charles-lyc/Pindar/hardware/datasheet/esp32/20200527125322933.jpg

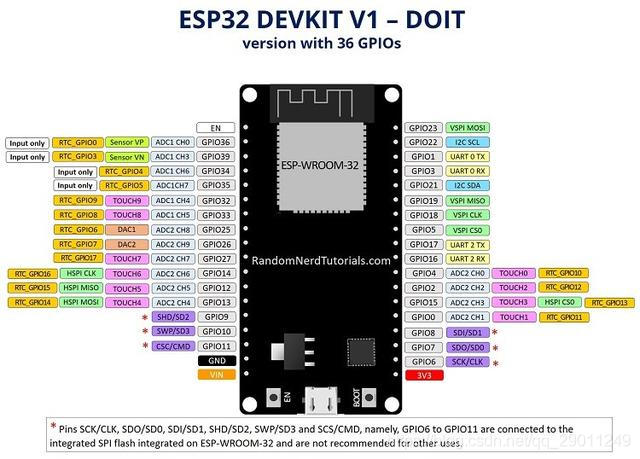
hardware/datasheet/esp32/20200527125322933.jpg
