charles-lyc/Pindar/hw/kicad/app/motor/dc_motor/dc_motor_x3.kicad_sch

## KiCad design hw/kicad/app/motor/dc_motor/dc_motor_x3.kicad_sch (2023-06-30)

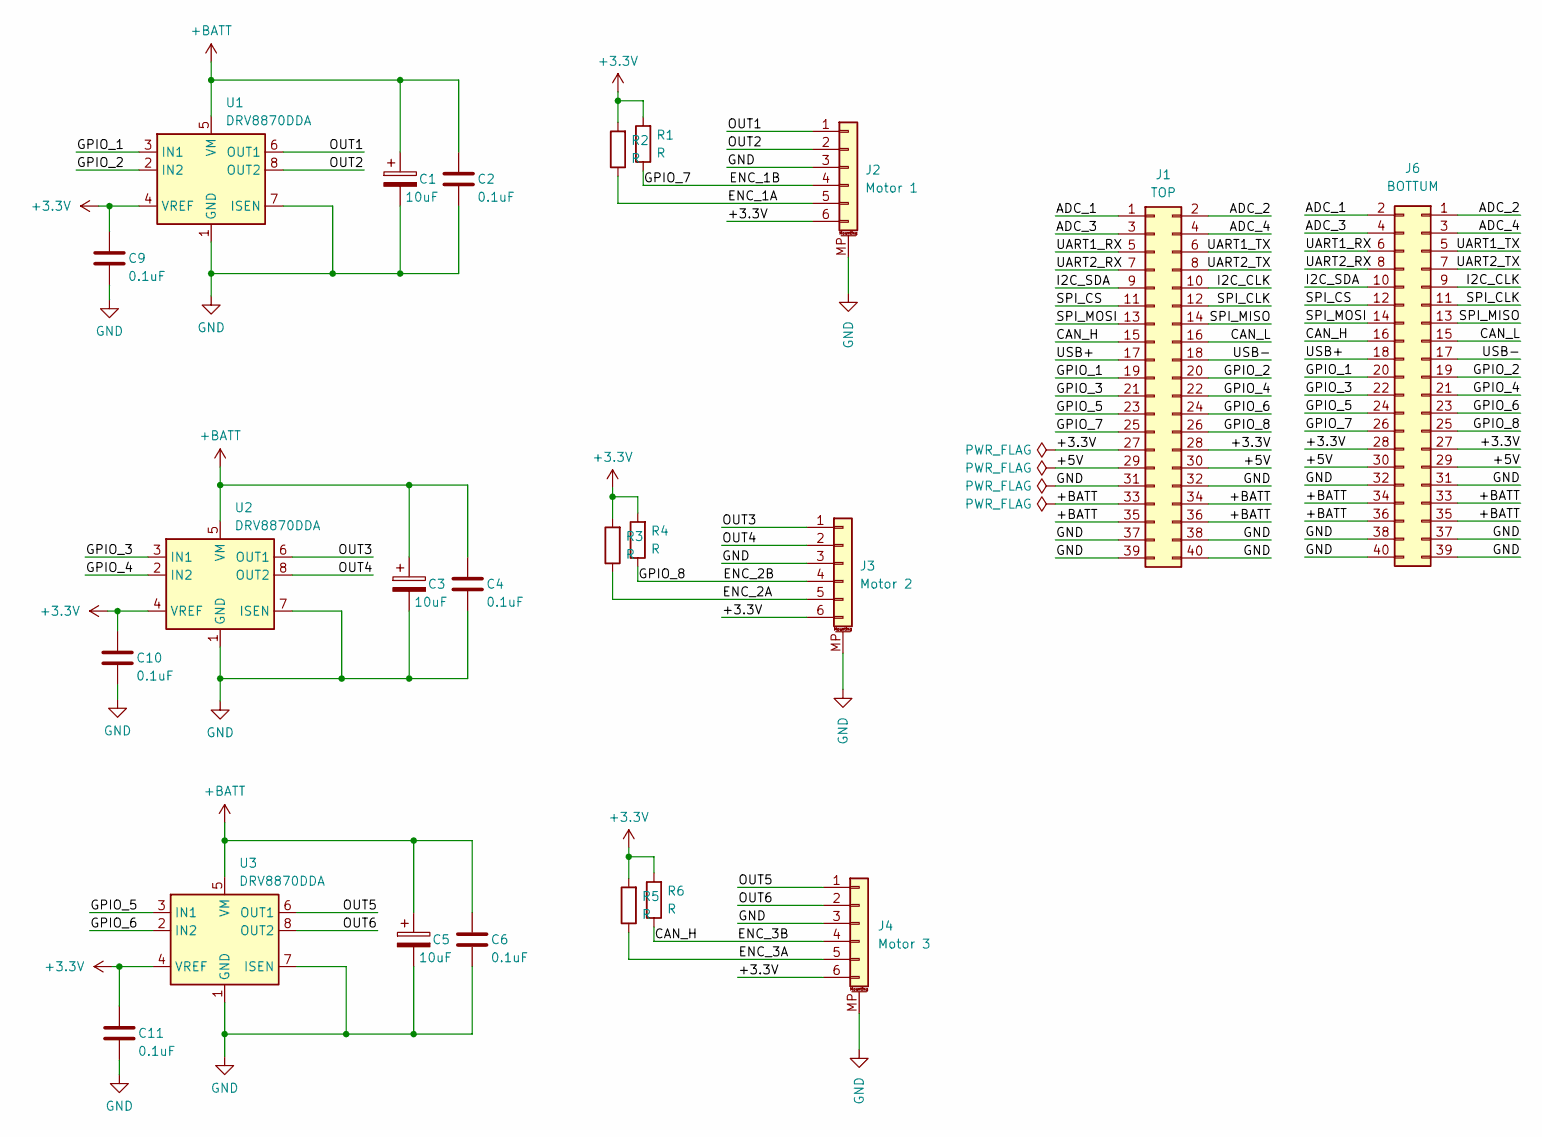
[picture p36: schematic dc_motor_x3.kicad_sch]

Parts:
C1, C3, C5: 10uF; CP_Elec_6.3x5.4
C2, C4, C6, C9, C10, C11: 0.1uF; C_0805_2012Metric
J1: TOP; PinHeader_2x20_P1.27mm_Vertical_SMD
J2: Motor 1; JST_GH_SM06B-GHS-TB_1x06-1MP_P1.25mm_Horizontal
J3: Motor 2; JST_GH_SM06B-GHS-TB_1x06-1MP_P1.25mm_Horizontal
J4: Motor 3; JST_GH_SM06B-GHS-TB_1x06-1MP_P1.25mm_Horizontal
J6: BOTTUM; PinHeader_2x20_P1.27mm_Vertical_SMD
R1, R2, R3, R4, R5, R6: R; R_0805_2012Metric
U1, U2, U3: DRV8870DDA; Texas_HTSOP-8-1EP_3.9x4.9mm_P1.27mm_EP2.95x4.9mm_Mask2.4x3.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

Connections:
+3.3V: C9.1, C10.1, C11.1, J1.27, J1.28, J2.6, J3.6, J4.6, J6.27, J6.28, R1.2, R2.2, R3.2, R4.2, R5.2, R6.2, U1.4 (VREF), U2.4 (VREF), U3.4 (VREF)
+5V: J1.29, J1.30, J6.29, J6.30
+BATT: C1.1, C2.1, C3.1, C4.1, C5.1, C6.1, J1.33, J1.34, J1.35, J1.36, J6.33, J6.34, J6.35, J6.36, U1.5 (VM), U2.5 (VM), U3.5 (VM)
ADC_1: J1.1, J6.2
ADC_2: J1.2, J6.1
ADC_3: J1.3, J6.4
ADC_4: J1.4, J6.3
CAN_H: J1.15, J4.4, J6.16, R6.1
CAN_L: J1.16, J6.15
ENC_1A: J2.5, R2.1
ENC_1B: J1.25, J2.4, J6.26, R1.1
ENC_2A: J3.5, R3.1
ENC_2B: J1.26, J3.4, J6.25, R4.1
ENC_3A: J4.5, R5.1
GND: C1.2, C2.2, C3.2, C4.2, C5.2, C6.2, C9.2, C10.2, C11.2, J1.31, J1.32, J1.37, J1.38, J1.39, J1.40, J2.3, J2.MP (MountPin), J3.3, J3.MP (MountPin), J4.3, J4.MP (MountPin), J6.31, J6.32, J6.37, J6.38, J6.39, J6.40, U1.1 (GND), U1.7 (ISEN), U1.9 (GND), U2.1 (GND), U2.7 (ISEN), U2.9 (GND), U3.1 (GND), U3.7 (ISEN), U3.9 (GND)
GPIO_1: J1.19, J6.20, U1.3 (IN1)
GPIO_2: J1.20, J6.19, U1.2 (IN2)
GPIO_3: J1.21, J6.22, U2.3 (IN1)
GPIO_4: J1.22, J6.21, U2.2 (IN2)
GPIO_5: J1.23, J6.24, U3.3 (IN1)
GPIO_6: J1.24, J6.23, U3.2 (IN2)
I2C_CLK: J1.10, J6.9
I2C_SDA: J1.9, J6.10
OUT1: J2.1, U1.6 (OUT1)
OUT2: J2.2, U1.8 (OUT2)
OUT3: J3.1, U2.6 (OUT1)
OUT4: J3.2, U2.8 (OUT2)
OUT5: J4.1, U3.6 (OUT1)
OUT6: J4.2, U3.8 (OUT2)
SPI_CLK: J1.12, J6.11
SPI_CS: J1.11, J6.12
SPI_MISO: J1.14, J6.13
SPI_MOSI: J1.13, J6.14
UART1_RX: J1.5, J6.6
UART1_TX: J1.6, J6.5
UART2_RX: J1.7, J6.8
UART2_TX: J1.8, J6.7
USB+: J1.17, J6.18
USB-: J1.18, J6.17
