charles-lyc/Pindar/firmware/components/module/imu.cpp

#include "freertos/FreeRTOS.h"
#include "freertos/task.h"
#include "freertos/semphr.h"

#include "esp_system.h"
#include "esp_log.h"

#include "imu.h"
#include "param.h"

IMU_Module::IMU_Module(IMU_Interface *itf)
{
	interface = itf;

	if (interface->probe()) {
		// throw std::invalid_argument("Value must be positive");
		while (1)
			;
	}
	interface->initialize();

	// create shared memory in iram
	// sm_data = (struct SM_ImuData *)malloc(sizeof(struct SM_ImuData));

	frame_event = xSemaphoreCreateBinary();

	// Note: 正在尝试直接将成员函数作为任务函数传递，而成员函数具有额外的隐式参数（即 this 指针），导致类型不匹配。这里的process_task方法是一个非静态成员函数，而非静态成员函数在调用时需要通过一个实例来访问
	// 方法一：使用静态中间函数并传递实例，这里其实是强行利用了xTaskCreate()可以给task带参这个设定，把实例当作参数传递进去
	xTaskCreate(&IMU_Module::process_task_static, "process_task", 4096, this, 3, &process_task_handle);
	// 方法二：使用std::bind
	// 方法三：lambda表达式（类似方法一）
	// xTaskCreate(CALLBACK_LAMBDA_VOID(IMU_Module, process_task), "process_task", 4096, this, 3, &process_task_handle);

}

IMU_Module::~IMU_Module()
{
	// interface.deinit(&interface);

	// xTaskDelete();
	// xSemaphoreDelete();
}

void IMU_Module::frame_event_isr(void *arg)
{
	timestamp = xTaskGetTickCountFromISR();
	// ESP_LOGI("IMU Module", "timestamp: %d", (uint32_t)timestamp);
	xSemaphoreGiveFromISR(frame_event, NULL);
}

void IMU_Module::process_task(void *pvParameters)
{
	while (1) {
		xSemaphoreTake(frame_event, 1);
		{
			// ll read
			if (interface->read_raw_data(gyro_raw, accel_raw, temperature_raw)) {
				ESP_LOGE("IMU Module", "read failed");
				continue;
			}

			pre_process();

			// madgwick complemental filter
			madgwick_update();
		}
	}
}

void IMU_Module::pre_process()
{
	// lpf
	for (size_t i = 0; i < 3; i++) {
		gyro_smooth[i] = gyro_raw[i];
		accel_smooth[i] = accel_raw[i];
	}

	// physical
	temperature = (float)temperature_raw[0] / 132.48 + 25;
	// ESP_LOGI("IMU Module", "raw gyro: %d %d %d", gyro_raw[0], gyro_raw[1], gyro_raw[2]);
	// ESP_LOGI("IMU Module", "raw accel: %d %d %d", accel_raw[0], accel_raw[1], accel_raw[2]);
	// ESP_LOGI("IMU Module", "raw temp: %f", temperature);
	// std::cout
	for (size_t i = 0; i < 3; i++) {
		gyro[i] = (gyro_smooth[i] - gyro_bias[i]) * gyro_scale[i];
		accel[i] = (accel_smooth[i] - accel_bias[i]) * accel_scale[i];
	}
}

void IMU_Module::madgwick_update()
{
}

void IMU_Module::gyro_static_calibr_task(void *pvParameters)
{
	TickType_t last_timestamp = 0;

	while (run_gyro_static_calibr) {
		if (timestamp != last_timestamp) {
			last_timestamp = timestamp;
		}

		vTaskDelay(100 / portTICK_PERIOD_MS);
	}

	// stop
}

void IMU_Module::gyro_z_scale_calibr_task(void *pvParameters)
{

	while (run_gyro_scale_calibr) {
		// calc gyro
		vTaskDelay(100 / portTICK_PERIOD_MS);
	}

	// stop
}

void IMU_Module::aceel_sphere_calibr_task(void *pvParameters)
{

	while (run_accel_calibr) {
		// calc gyro
		vTaskDelay(100 / portTICK_PERIOD_MS);
	}

	// stop
}
